Collector3/modular-camera-case/Camera Case for v2 Camera.stl

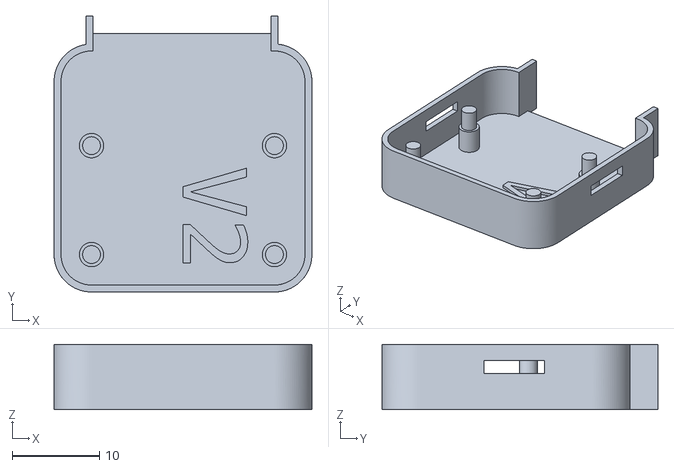
[picture p16: CAD file, 2017-04-17]
Camera Case for v2 Camera.stl
29.6 x 31.7 x 7.50
