Collector3/modular-camera-case/Long Center Case.stl

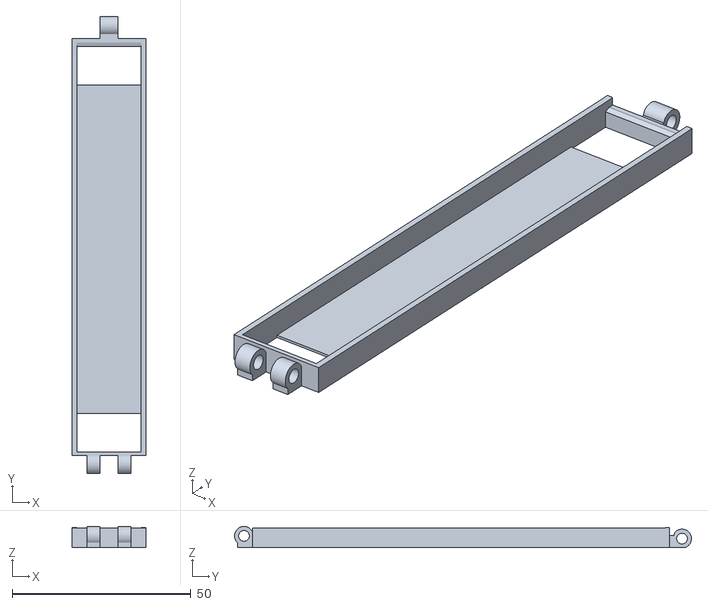
[picture p17: CAD file, 2017-04-17]
Long Center Case.stl
20.6 x 127.7 x 5.90
