Collector3/modular-camera-case/Pi Zero Holder.stl

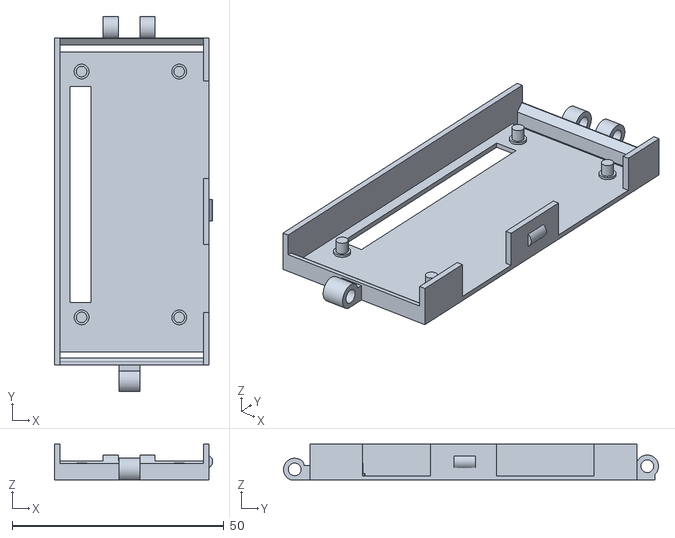
[picture p18: CAD file, 2017-04-17]
Pi Zero Holder.stl
37.4 x 88.5 x 8.50
