Collector3/modular-camera-case/Center Case.stl

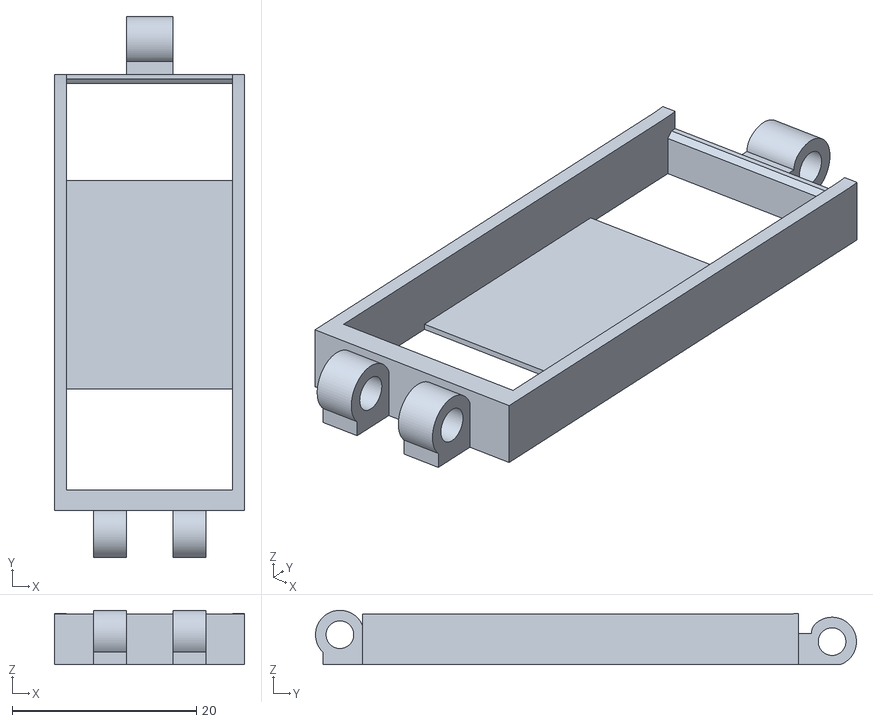
[picture p19: CAD file, 2017-04-17]
Center Case.stl
20.6 x 58.7 x 5.90
